ataberkciftlikli/fezai-2/Flight Computer v1.2/main_flight_computer_front.png

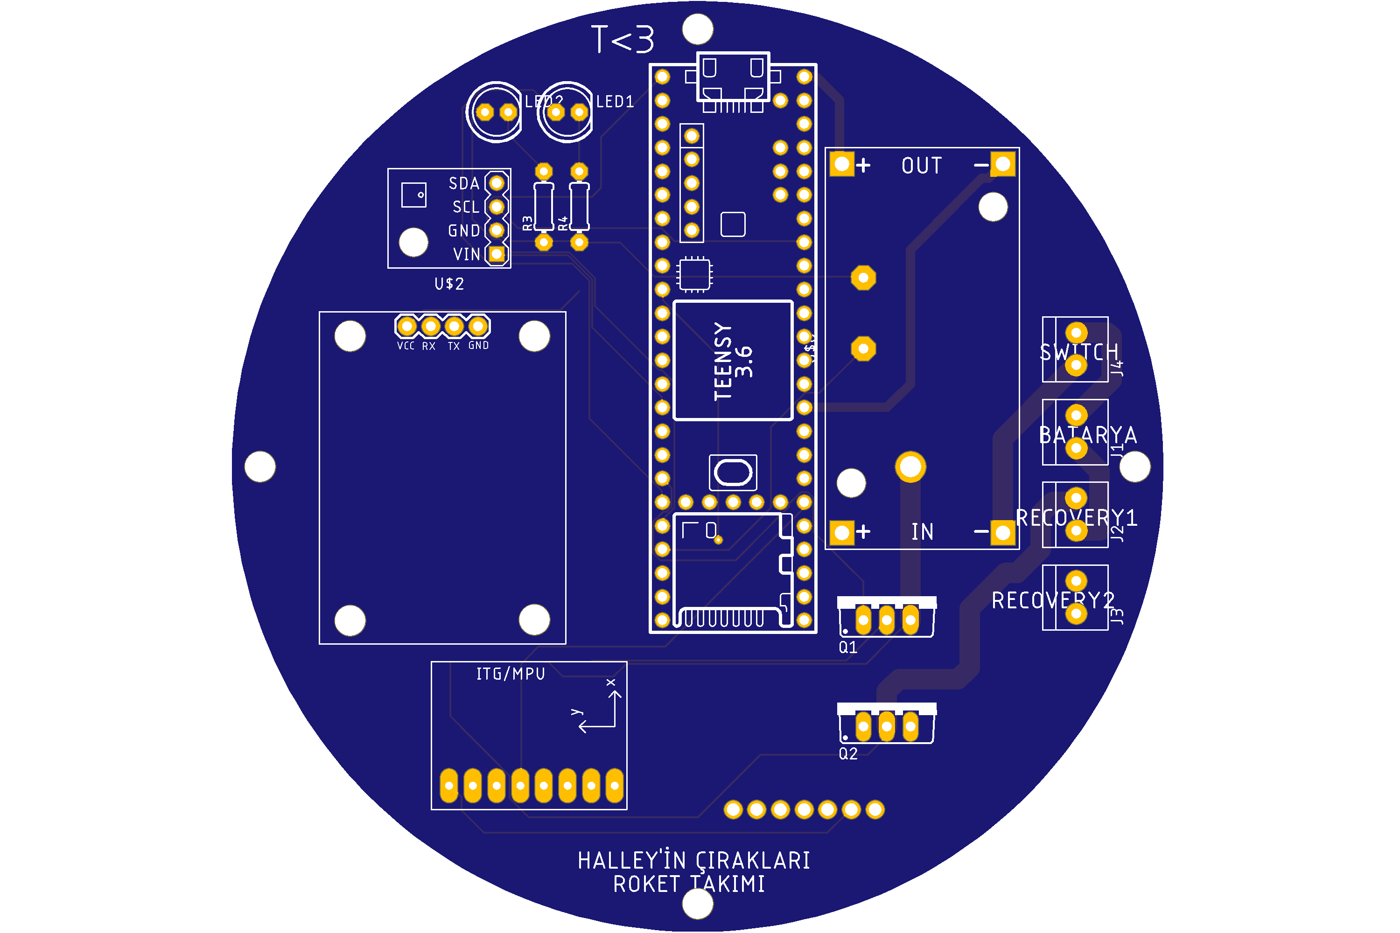
Flight Computer v1.2/main_flight_computer_front.png
