ataberkciftlikli/fezai-2/Second Flight Computer/second_flight_computer.png

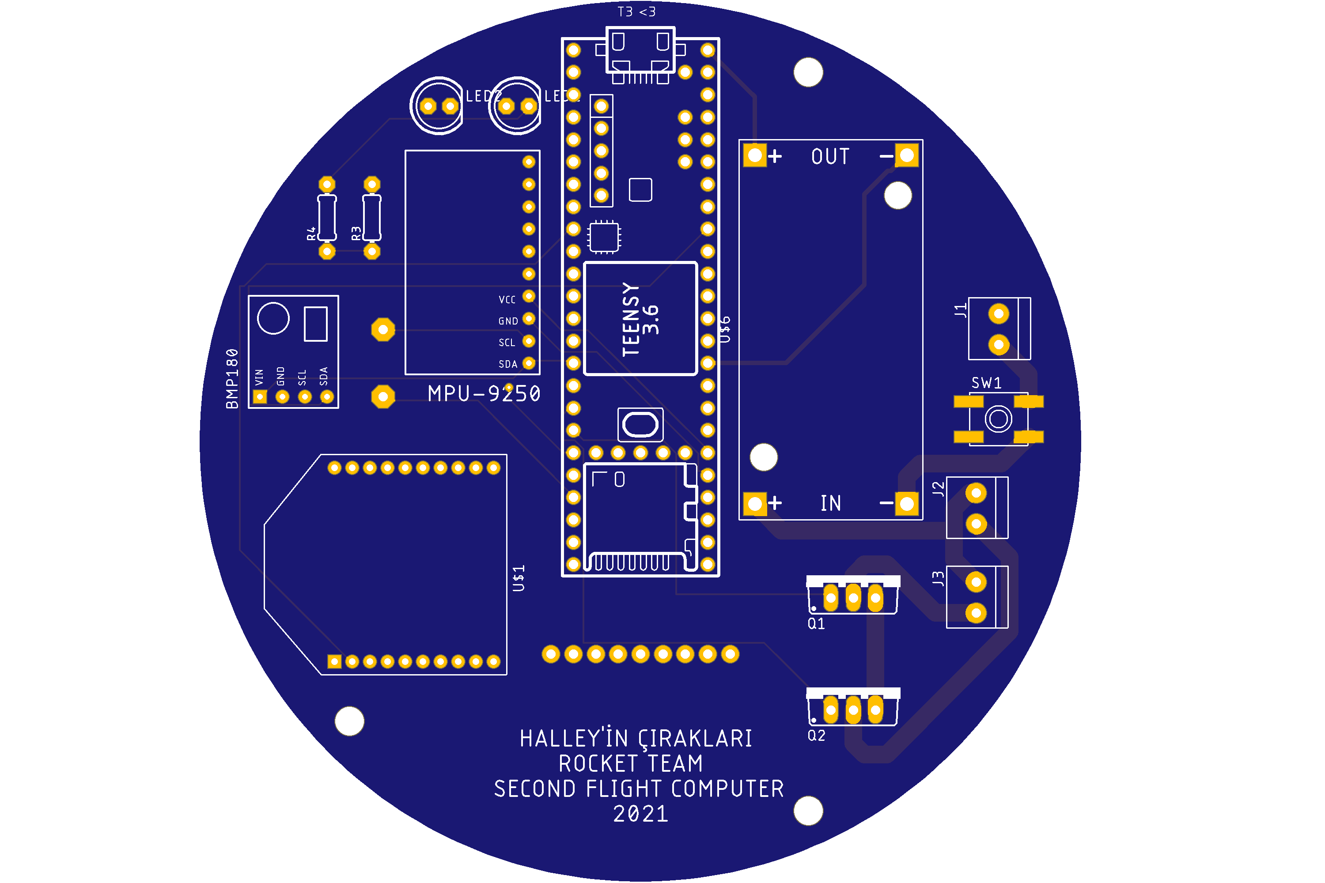
Second Flight Computer/second_flight_computer.png
